s-voelkl/LumenTrace/3d-models/stl/building_t9.stl

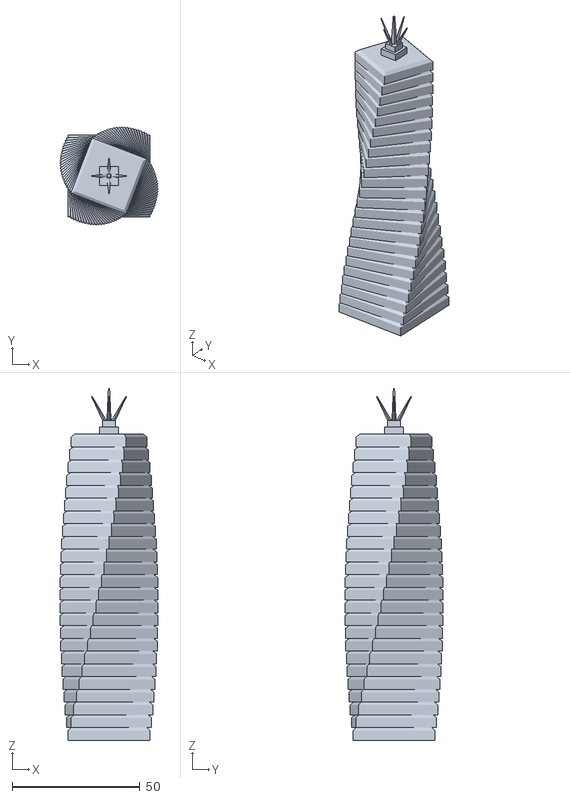
[picture p34: CAD file, 2026-07-07]
3d-models/stl/building_t9.stl
38.5 x 38.5 x 138.0
