s-voelkl/LumenTrace/3d-models/stl/sf_chimney.stl

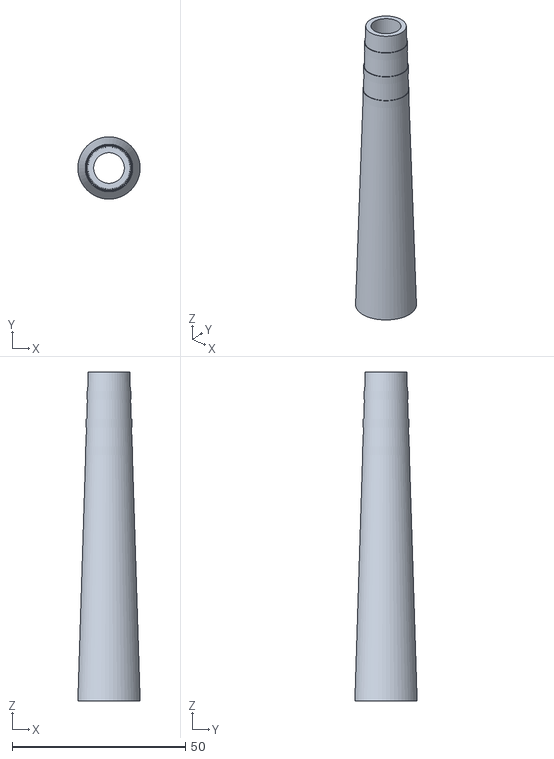
[picture p35: CAD file, 2026-07-07]
3d-models/stl/sf_chimney.stl
18.0 x 18.0 x 95.0
