s-voelkl/LumenTrace/3d-models/stl/lamp_b.stl

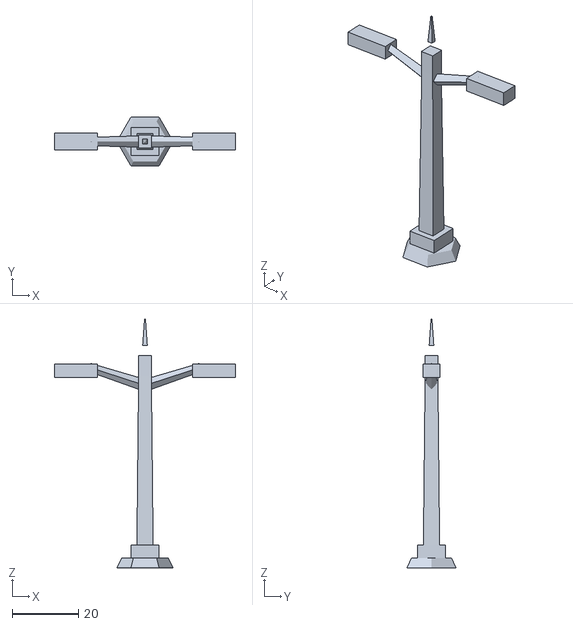
[picture p36: CAD file, 2026-07-07]
3d-models/stl/lamp_b.stl
54.6 x 14.7 x 75.0
