s-voelkl/LumenTrace/3d-models/stl/building_t2.stl

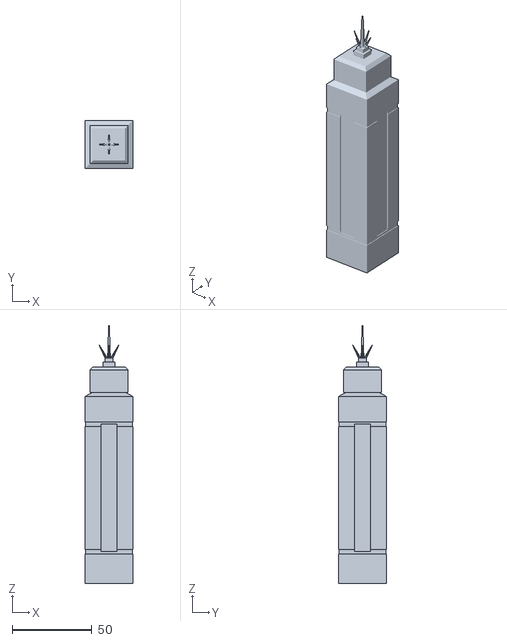
[picture p37: CAD file, 2026-07-07]
3d-models/stl/building_t2.stl
30.0 x 30.0 x 162.0
