s-voelkl/LumenTrace/3d-models/stl/sf_pylon.stl

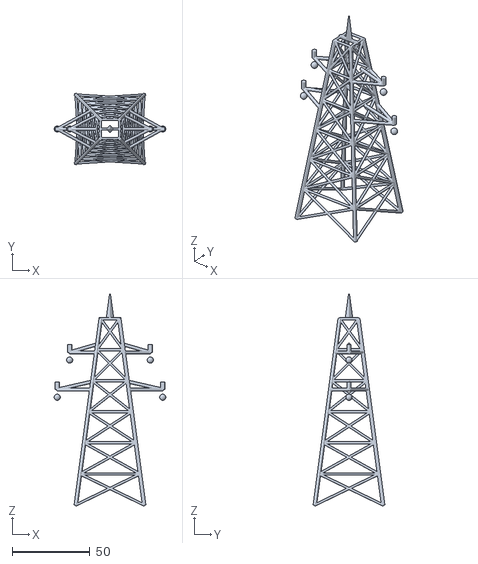
[picture p38: CAD file, 2026-07-07]
3d-models/stl/sf_pylon.stl
72.0 x 46.3 x 136.7
