s-voelkl/LumenTrace/3d-models/stl/building_t10.stl

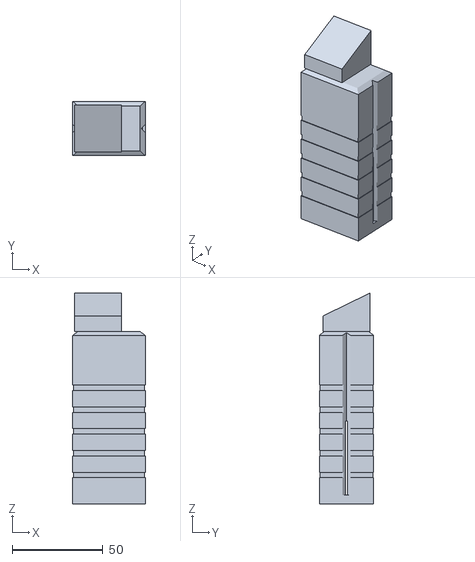
[picture p39: CAD file, 2026-07-07]
3d-models/stl/building_t10.stl
40.0 x 30.0 x 116.3
