s-voelkl/LumenTrace/3d-models/stl/lamp_c.stl

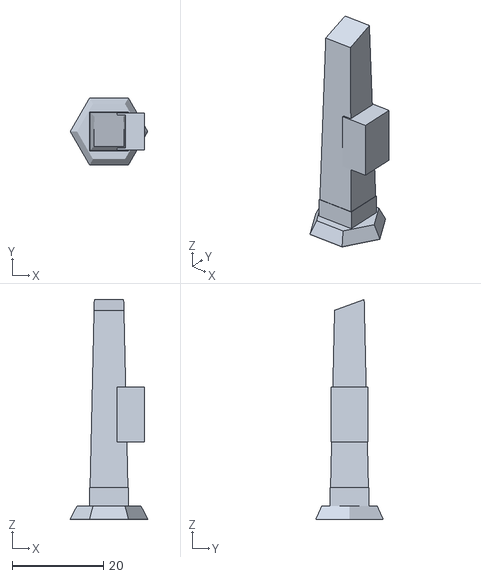
[picture p40: CAD file, 2026-07-07]
3d-models/stl/lamp_c.stl
17.0 x 14.7 x 48.2
