s-voelkl/LumenTrace/3d-models/stl/subwoofer_baseplate.stl

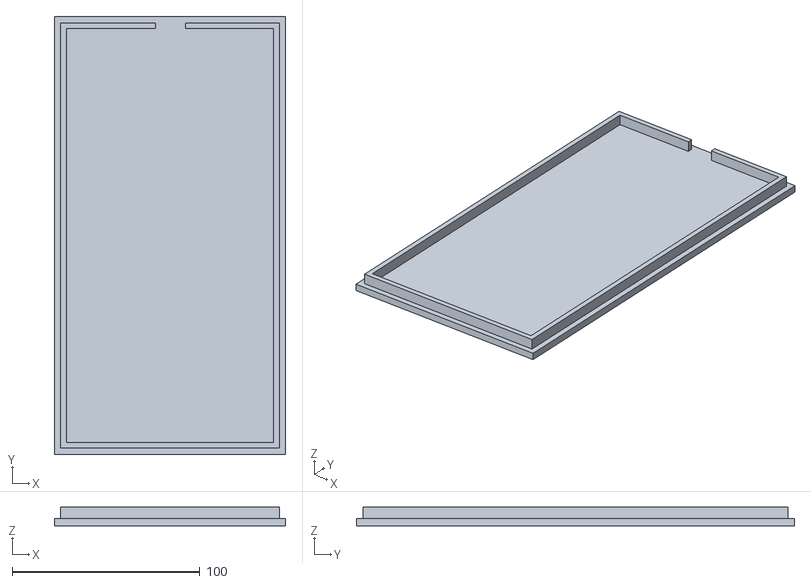
[picture p41: CAD file, 2026-06-19]
3d-models/stl/subwoofer_baseplate.stl
123.0 x 233.0 x 10.0
