s-voelkl/LumenTrace/3d-models/stl/satellite_lower.stl

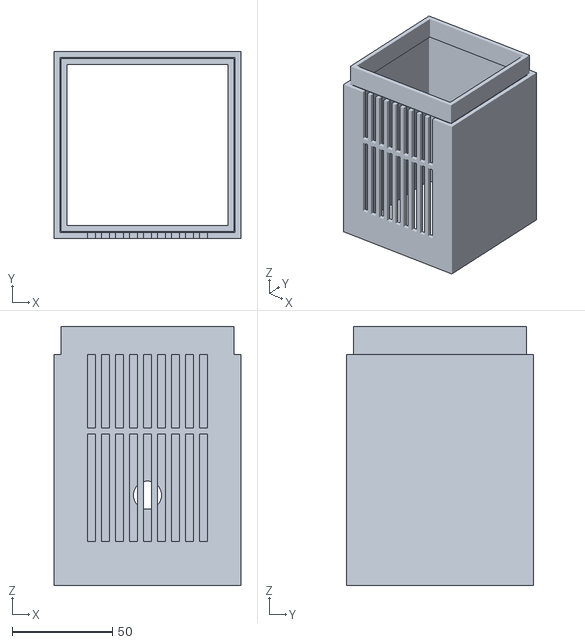
[picture p42: CAD file, 2026-06-19]
3d-models/stl/satellite_lower.stl
93.0 x 93.0 x 129.0
