s-voelkl/LumenTrace/3d-models/stl/subwoofer_upper.stl

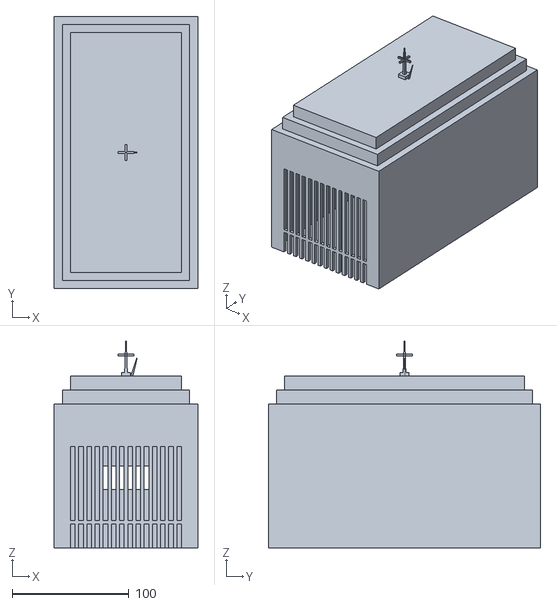
[picture p43: CAD file, 2026-06-19]
3d-models/stl/subwoofer_upper.stl
123.0 x 233.0 x 177.0
