s-voelkl/LumenTrace/3d-models/stl/subwoofer_lower.stl

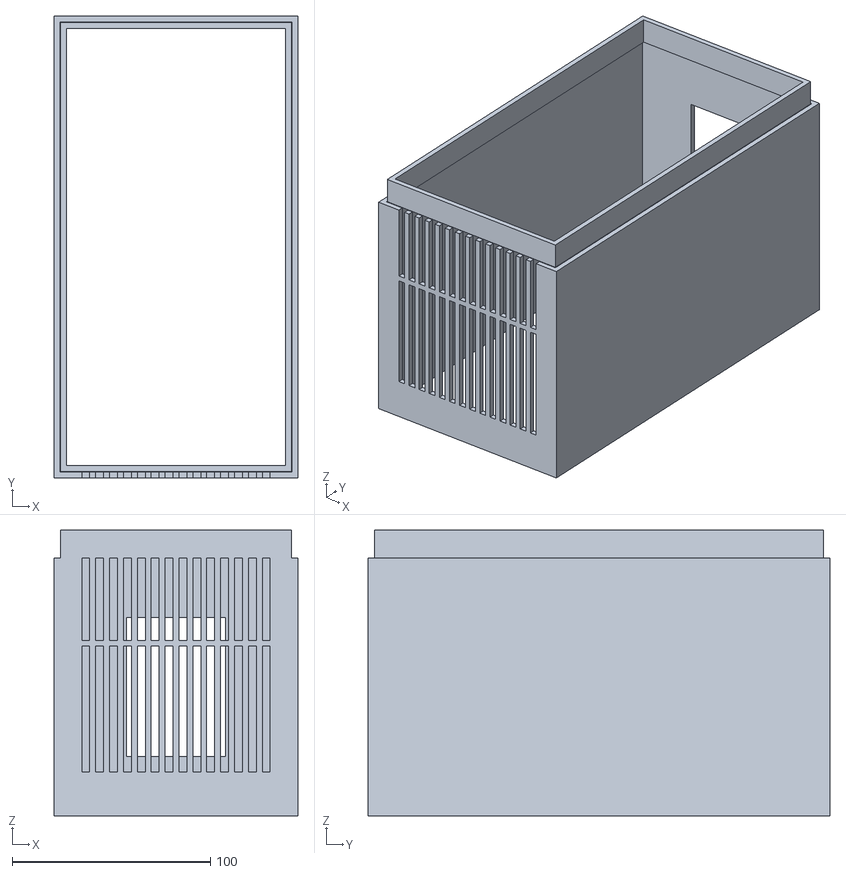
[picture p44: CAD file, 2026-06-19]
3d-models/stl/subwoofer_lower.stl
123.0 x 233.0 x 144.0
