s-voelkl/LumenTrace/3d-models/stl/satellite_baseplate.stl

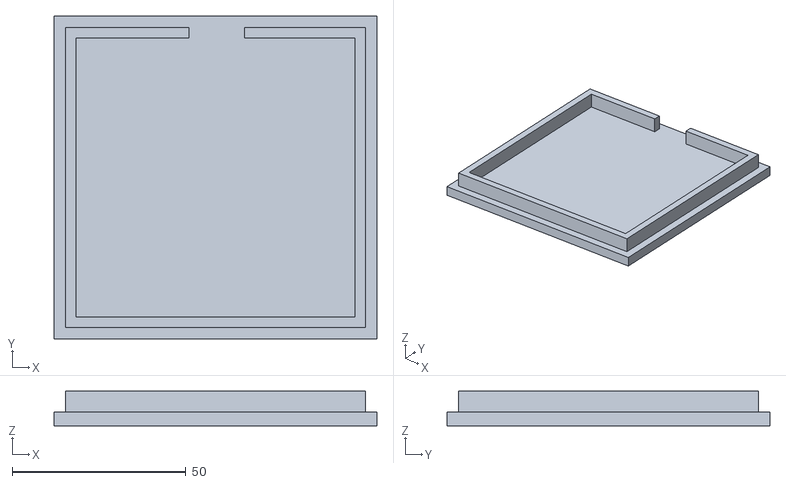
[picture p45: CAD file, 2026-06-19]
3d-models/stl/satellite_baseplate.stl
93.0 x 93.0 x 10.0
