s-voelkl/LumenTrace/3d-models/stl/satellite_upper.stl

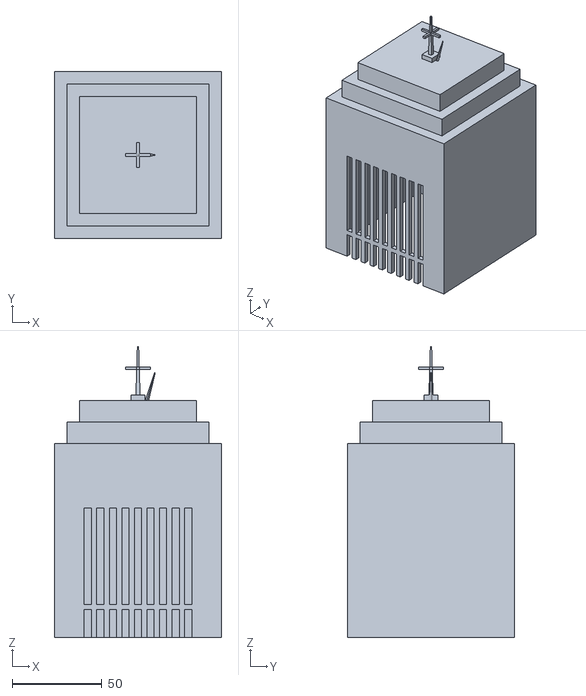
[picture p46: CAD file, 2026-06-19]
3d-models/stl/satellite_upper.stl
93.0 x 93.0 x 162.0
