s-voelkl/LumenTrace/3d-models/stl/LED_Clip_CarreraGo.stl

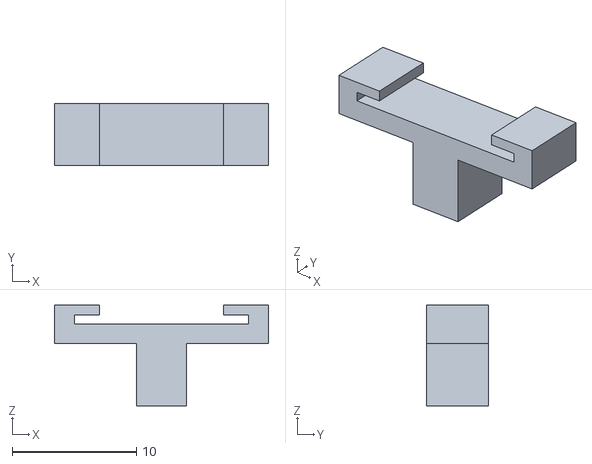
[picture p47: CAD file, 2026-04-20]
3d-models/stl/LED_Clip_CarreraGo.stl
17.2 x 5.00 x 8.10
